angelinakrinos/lab64_vday/lab64_vday_musicbox/battery-holder-4/Renderings/KEYELCO_1043.JPG

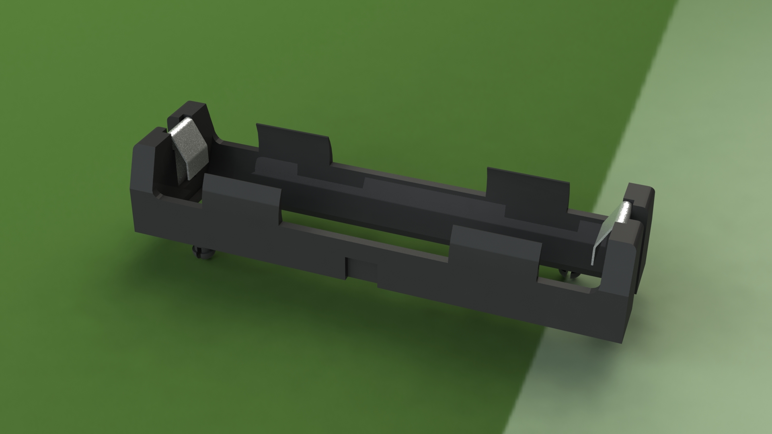
lab64_vday_musicbox/battery-holder-4/Renderings/KEYELCO_1043.JPG
