angelinakrinos/lab64_vday/lab64_vday_musicbox/battery-holder-4/Renderings/KEYELCO_1043_with_NCR-18650B.93.jpg

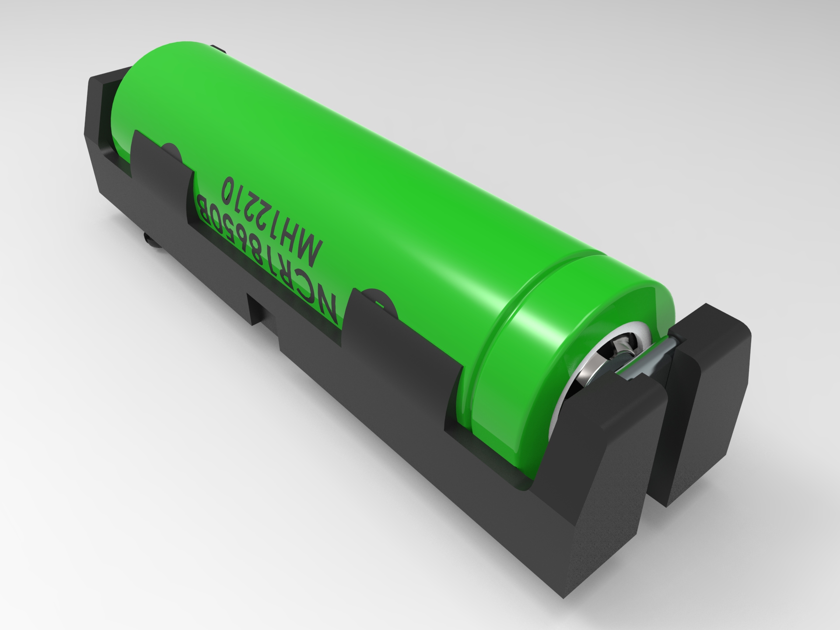
lab64_vday_musicbox/battery-holder-4/Renderings/KEYELCO_1043_with_NCR-18650B.93.jpg
