angelinakrinos/lab64_vday/lab64_vday_musicbox/terminal-block-2p-5mm-1/Terminal Block 5mm.png

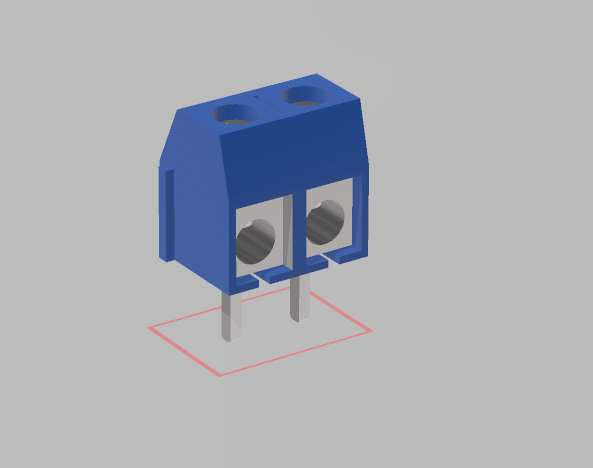
lab64_vday_musicbox/terminal-block-2p-5mm-1/Terminal Block 5mm.png
