angelinakrinos/lab64_vday/ref_photos/green_board_pics/green_board_layout.jpg

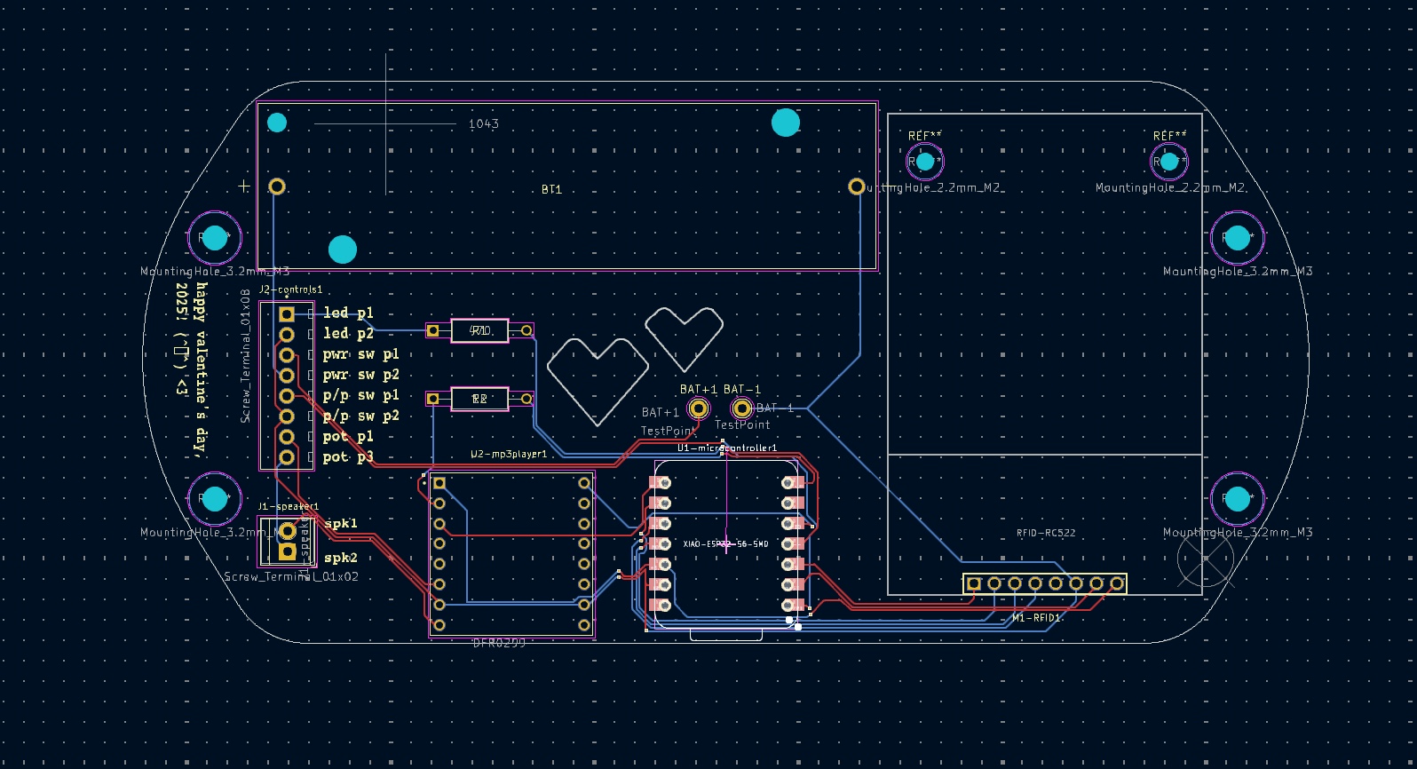
ref_photos/green_board_pics/green_board_layout.jpg
