angelinakrinos/lab64_vday/structure/Valentines Box v3/support 1.dxf

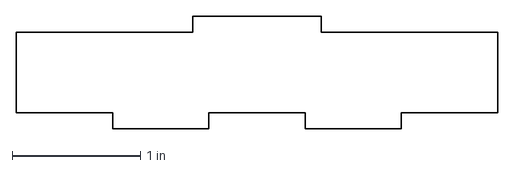
[picture p23: CAD file, 2025-02-14]
structure/Valentines Box v3/support 1.dxf
3.75 x 0.875 in
