angelinakrinos/lab64_vday/structure/Valentines Box v3/bottom.dxf

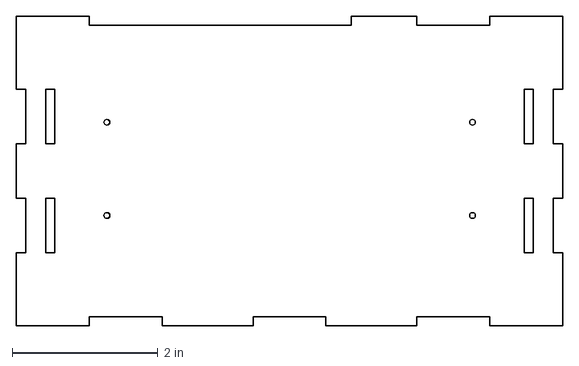
[picture p24: CAD file, 2025-02-14]
structure/Valentines Box v3/bottom.dxf
7.50 x 4.25 in
