angelinakrinos/lab64_vday/structure/Valentines Box v3/id card holder.dxf

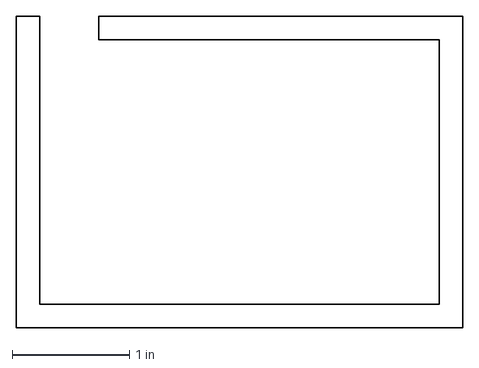
[picture p25: CAD file, 2025-02-14]
structure/Valentines Box v3/id card holder.dxf
3.80 x 2.65 in
