angelinakrinos/lab64_vday/structure/Valentines Box v3/second floor.dxf

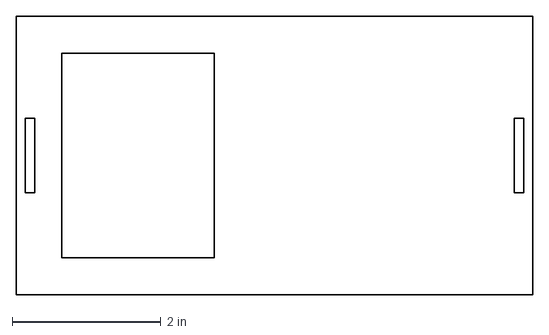
[picture p26: CAD file, 2025-02-14]
structure/Valentines Box v3/second floor.dxf
6.95 x 3.75 in
