angelinakrinos/lab64_vday/structure/Valentines Box v3/Left wall.dxf

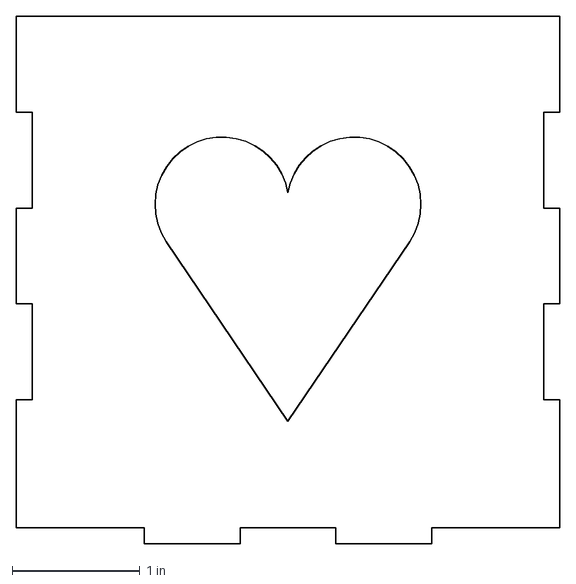
[picture p27: CAD file, 2025-02-14]
structure/Valentines Box v3/Left wall.dxf
4.25 x 4.12 in
